miketronic/brkn-keyboard/images/20240415_103638.jpg

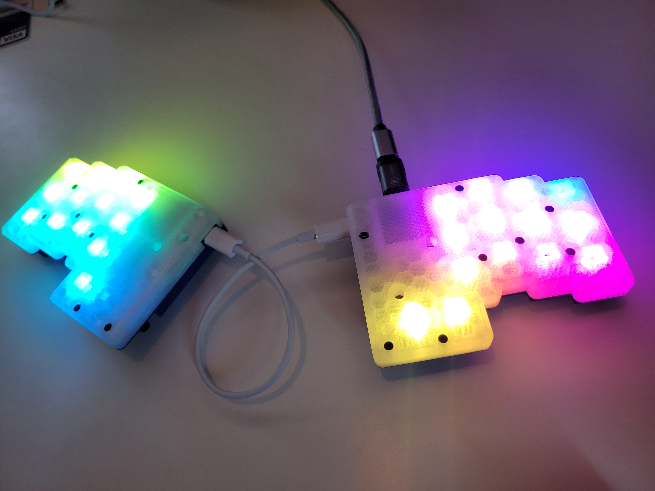
images/20240415_103638.jpg
