miketronic/brkn-keyboard/images/20240415_103808.jpg

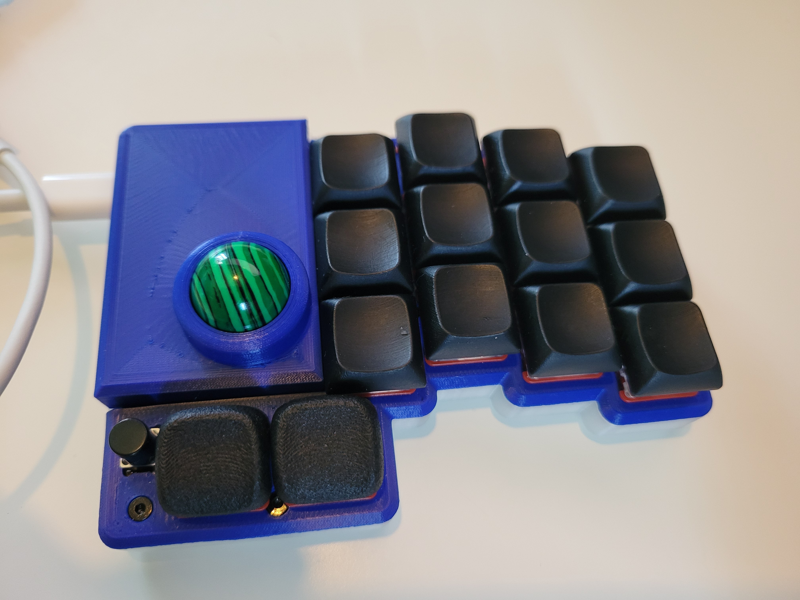
images/20240415_103808.jpg
