miketronic/brkn-keyboard/images/20240416_134642.jpg

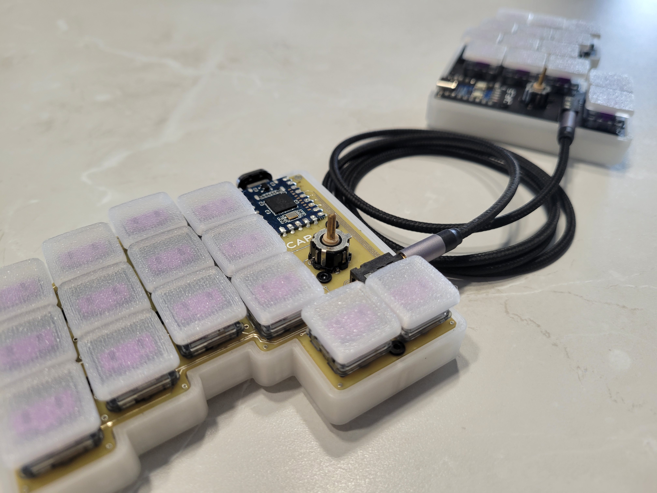
images/20240416_134642.jpg
