miketronic/brkn-keyboard/images/20240416_151212.jpg

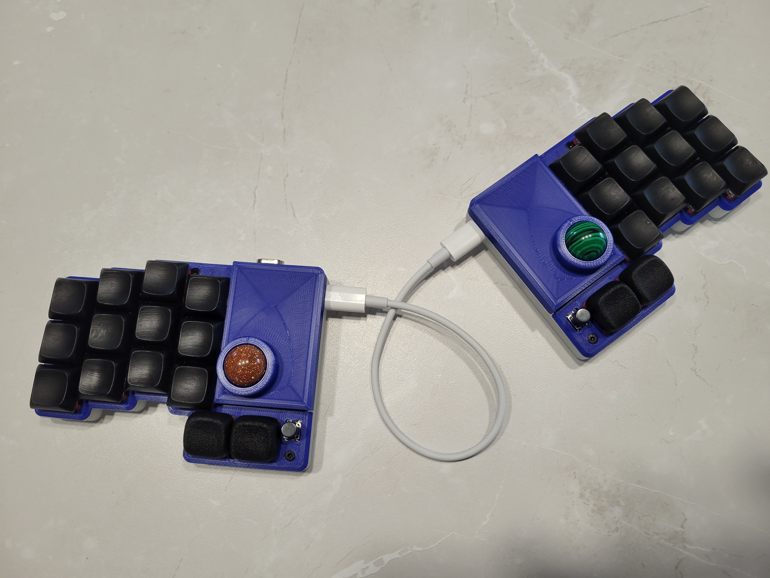
images/20240416_151212.jpg
