miketronic/brkn-keyboard/images/20240416_151223.jpg

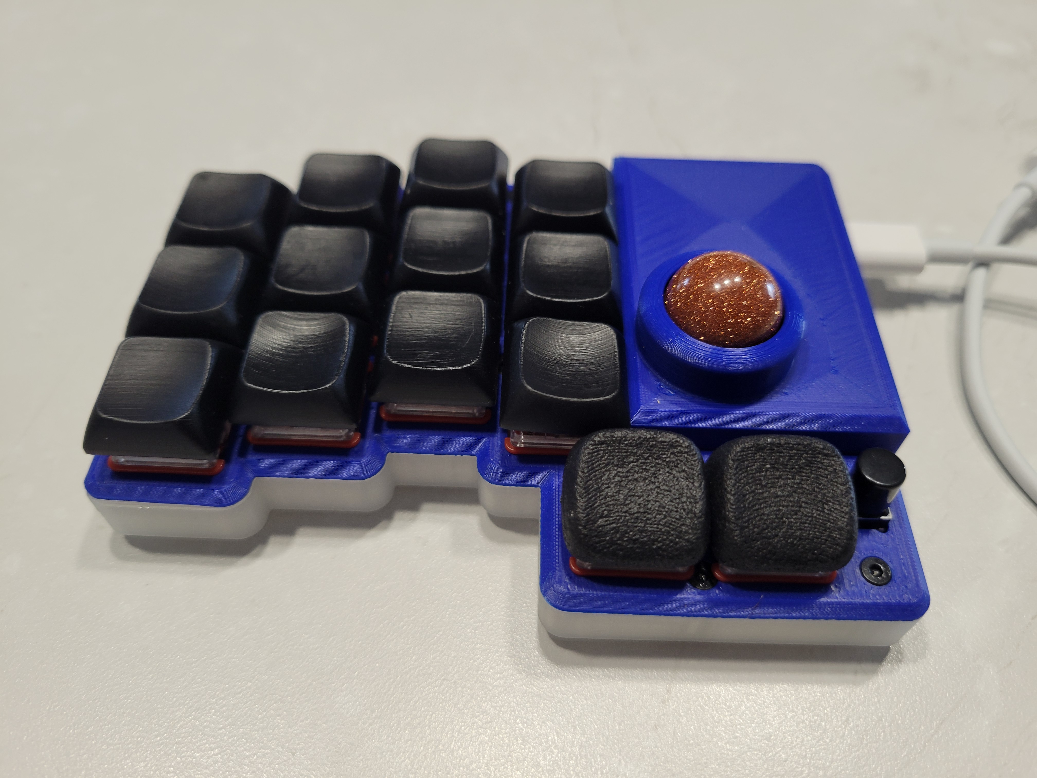
images/20240416_151223.jpg
